SandpiperElectronics/Z80DigitalClock/Images/Testing RTC (4:6:20).JPG

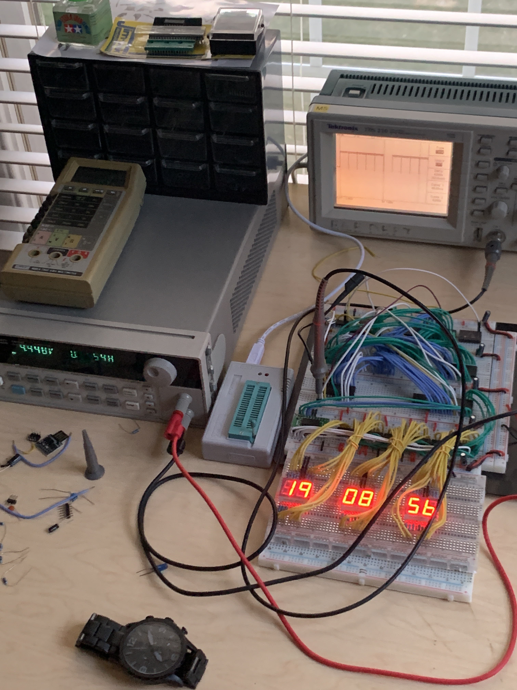
Images/Testing RTC (4:6:20).JPG
