SandpiperElectronics/Z80DigitalClock/Images/Test Using Hex Display and PIO (2:11:20).JPG

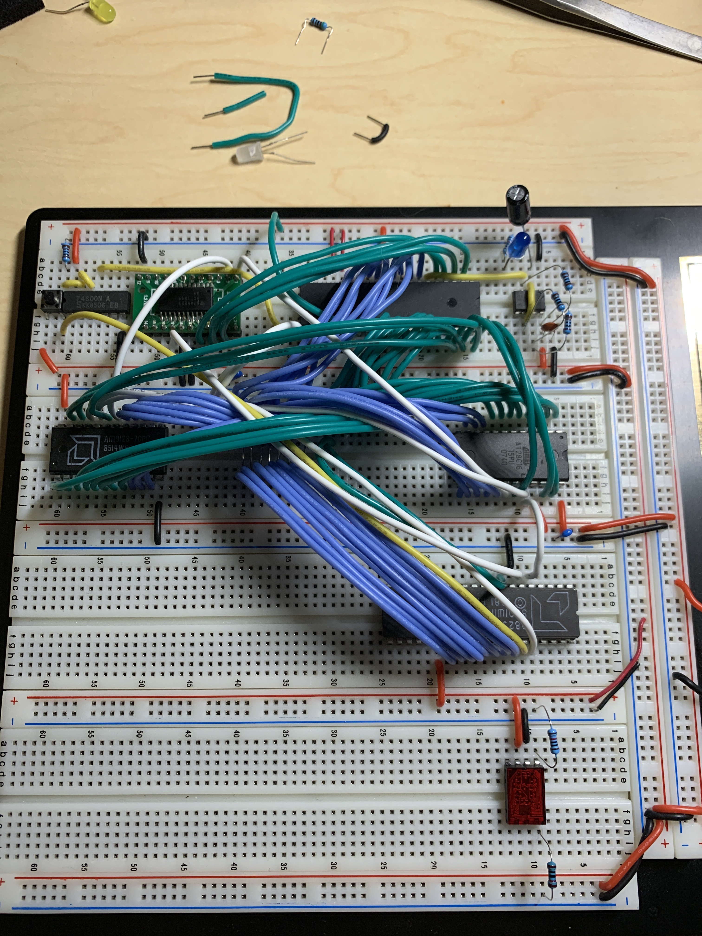
Images/Test Using Hex Display and PIO (2:11:20).JPG
